kotoMJ/kotiheating-arduino/extras/photos/IMG_20170921_204654.jpg

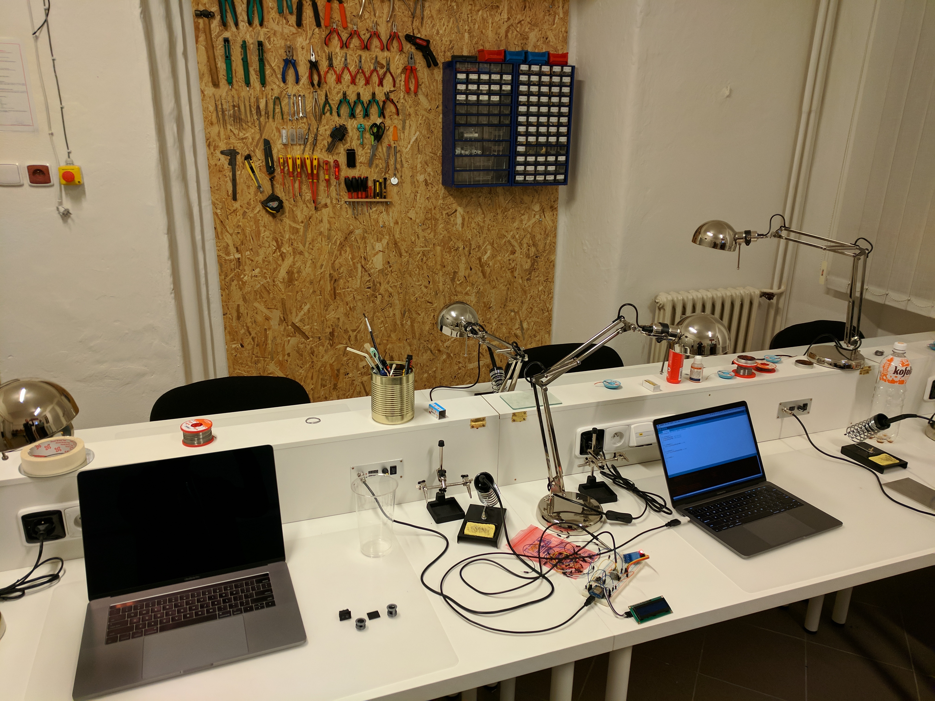
extras/photos/IMG_20170921_204654.jpg
