kotoMJ/kotiheating-arduino/extras/photos/IMG_20170921_204710.jpg

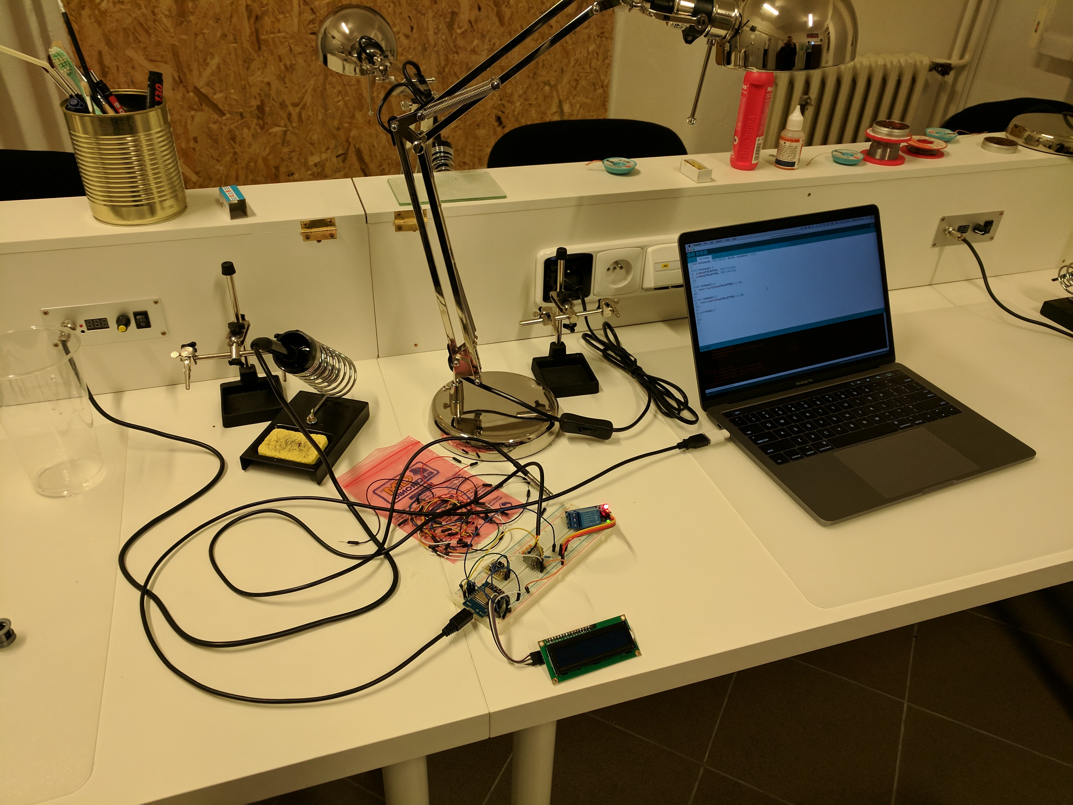
extras/photos/IMG_20170921_204710.jpg
