kotoMJ/kotiheating-arduino/extras/photos/IMG_20171009_110615.jpg

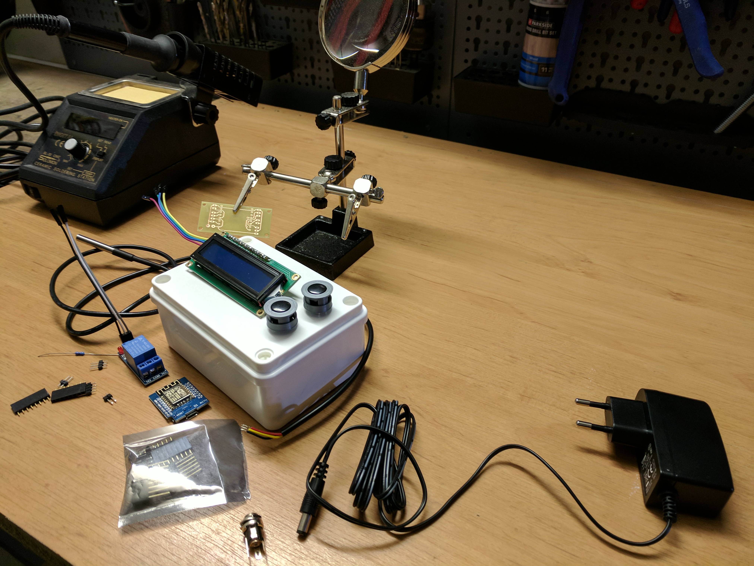
extras/photos/IMG_20171009_110615.jpg
