kotoMJ/kotiheating-arduino/extras/photos/IMG_20171016_214303.jpg

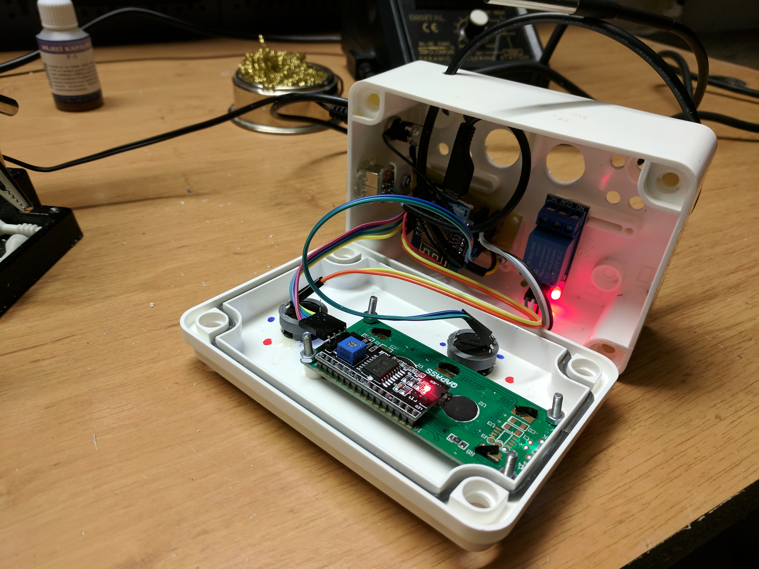
extras/photos/IMG_20171016_214303.jpg
