kotoMJ/kotiheating-arduino/extras/photos/IMG_20171016_214608.jpg

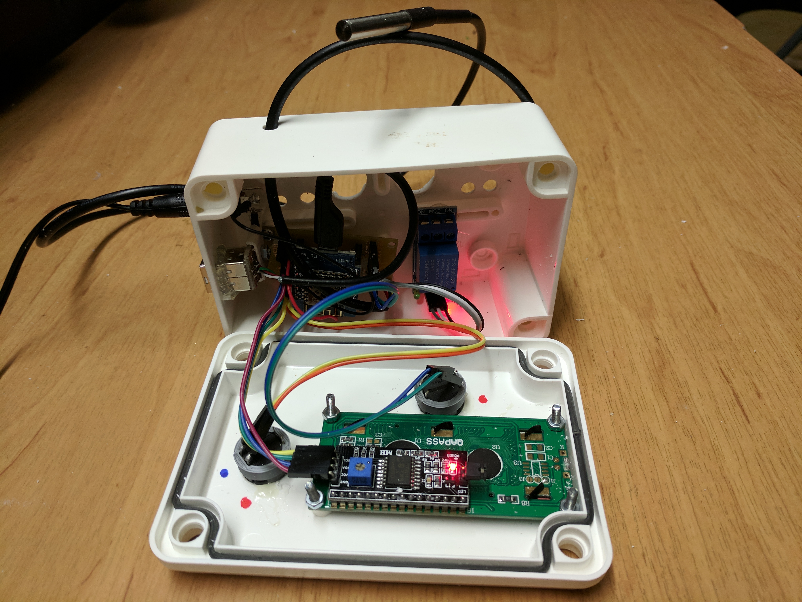
extras/photos/IMG_20171016_214608.jpg
