kotoMJ/kotiheating-arduino/extras/photos/IMG_20171016_214859.jpg

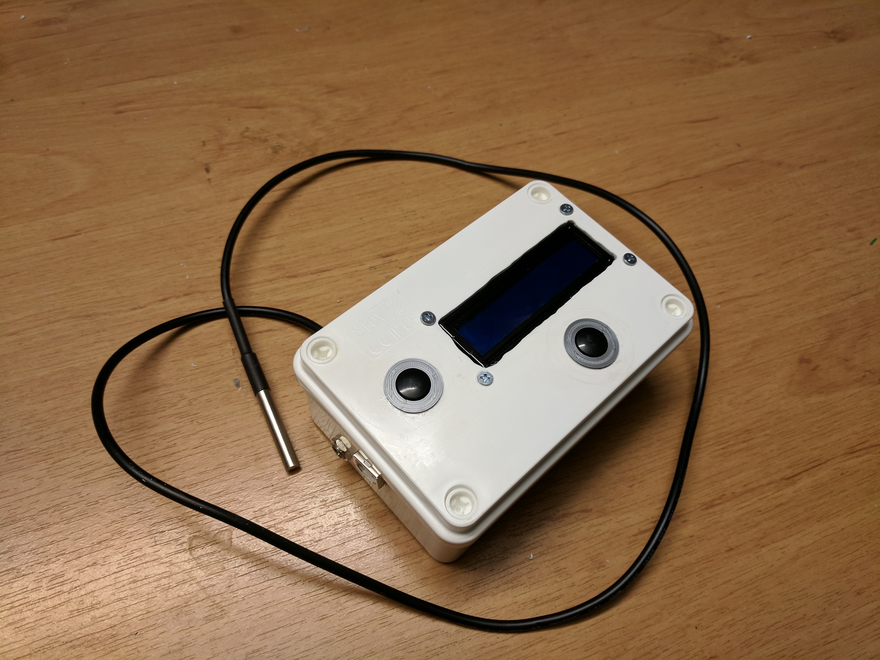
extras/photos/IMG_20171016_214859.jpg
