kotoMJ/kotiheating-arduino/extras/photos/IMG_20171016_214953.jpg

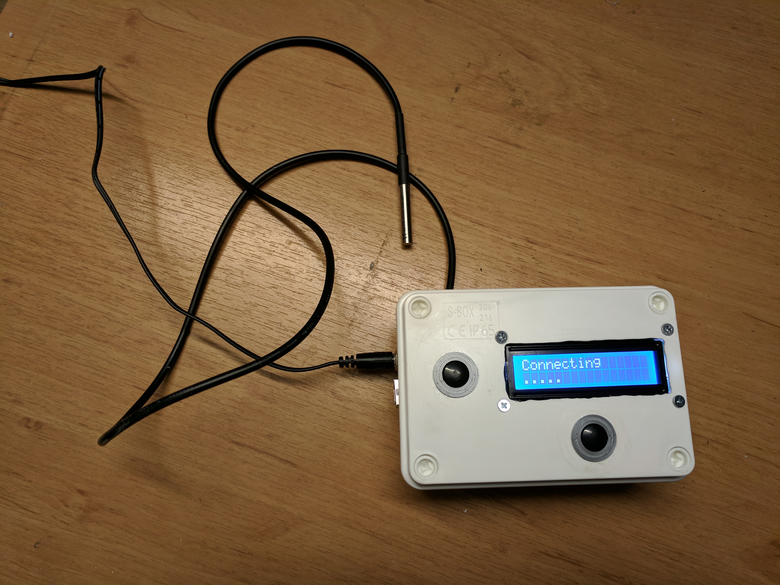
extras/photos/IMG_20171016_214953.jpg
